ericpearson1313/fpga_rocket_launcher/forge_launcher/forgearch.jpg

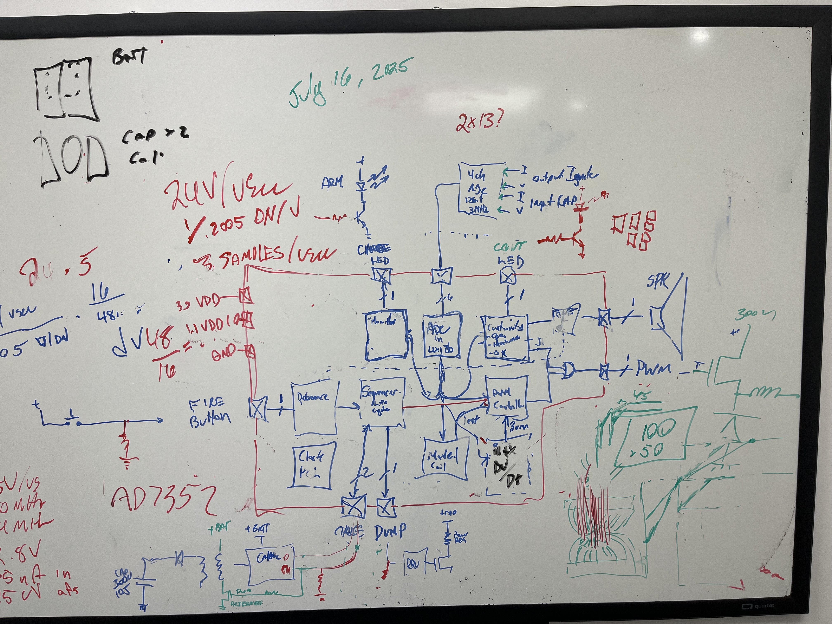
forge_launcher/forgearch.jpg
